Daxxn/BenchyReloaded/Docs/Renders/MotherBoard/BenchyMotherBoard-PCB_Early2-BOT1.png

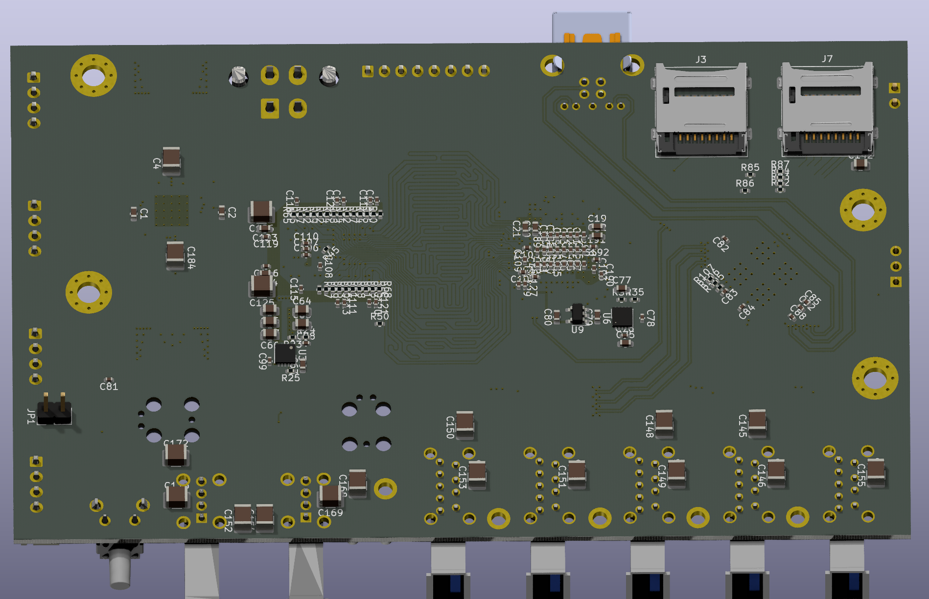
Docs/Renders/MotherBoard/BenchyMotherBoard-PCB_Early2-BOT1.png
