Daxxn/BenchyReloaded/Docs/Renders/MotherBoard/BenchyMotherBoard-PCB_Early3-TOP1.png

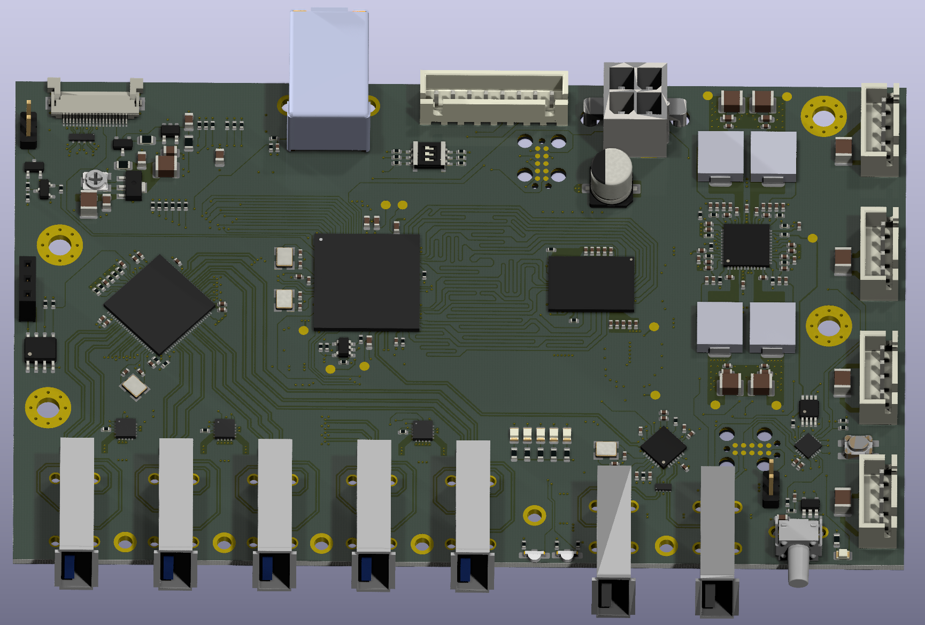
Docs/Renders/MotherBoard/BenchyMotherBoard-PCB_Early3-TOP1.png
