Daxxn/BenchyReloaded/Docs/Renders/MotherBoard/BenchyMotherBoard-PCB_Early-TOP1.png

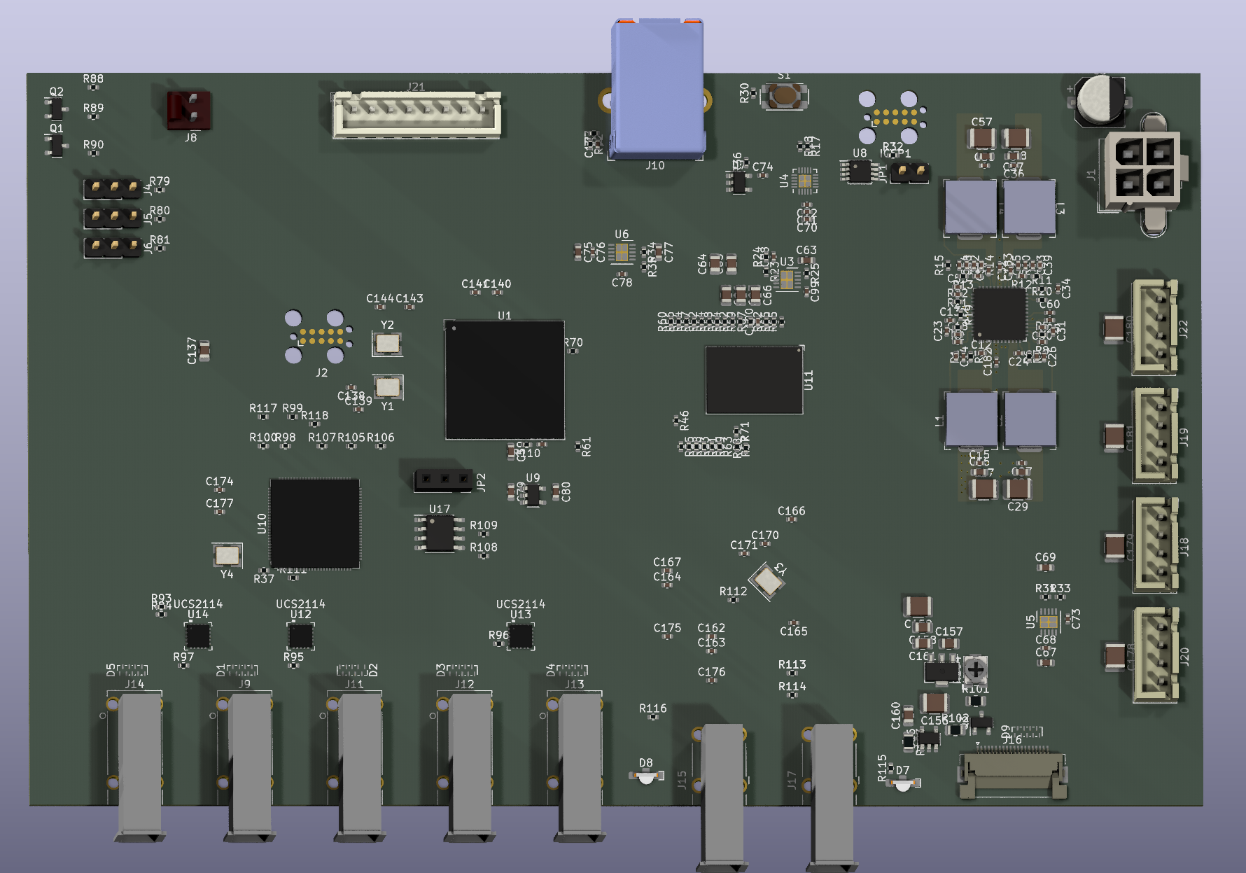
Docs/Renders/MotherBoard/BenchyMotherBoard-PCB_Early-TOP1.png
