Daxxn/BenchyReloaded/Docs/Renders/MotherBoard/BenchyMotherBoard-REV1-MPU.png

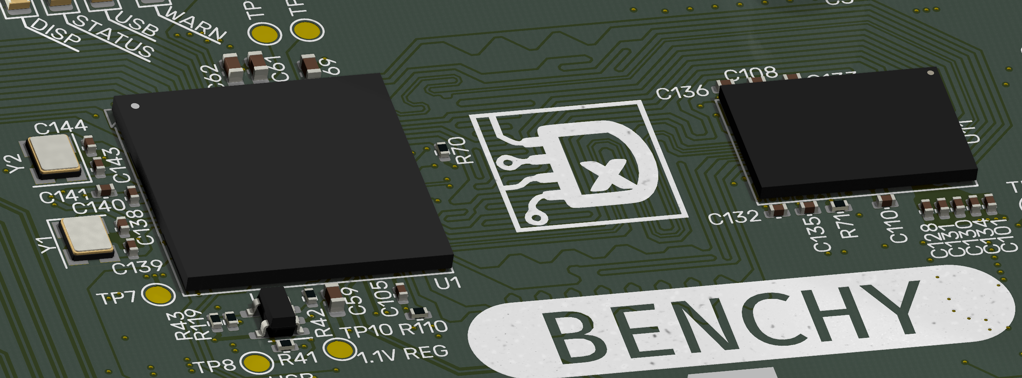
Docs/Renders/MotherBoard/BenchyMotherBoard-REV1-MPU.png
