Daxxn/BenchyReloaded/Docs/Renders/MyPain/BenchyMotherBoard-PCB.png

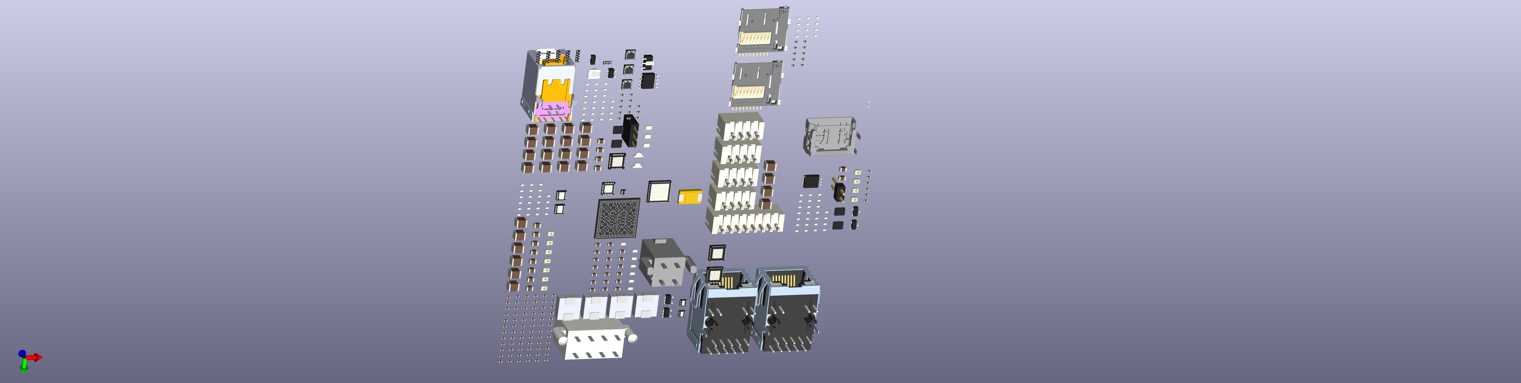
Docs/Renders/MyPain/BenchyMotherBoard-PCB.png
