Daxxn/BenchyReloaded/Docs/Renders/MyPain/JustThePS.JPG

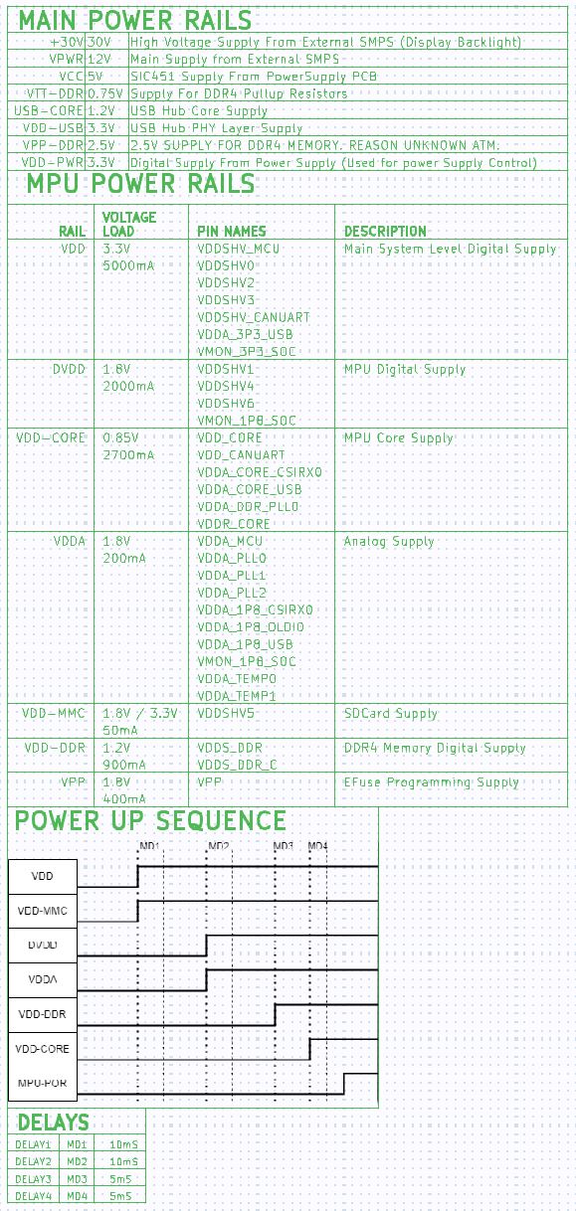
Docs/Renders/MyPain/JustThePS.JPG
