Daxxn/BenchyReloaded/Docs/Renders/Version2/Benchy-Front1.JPG

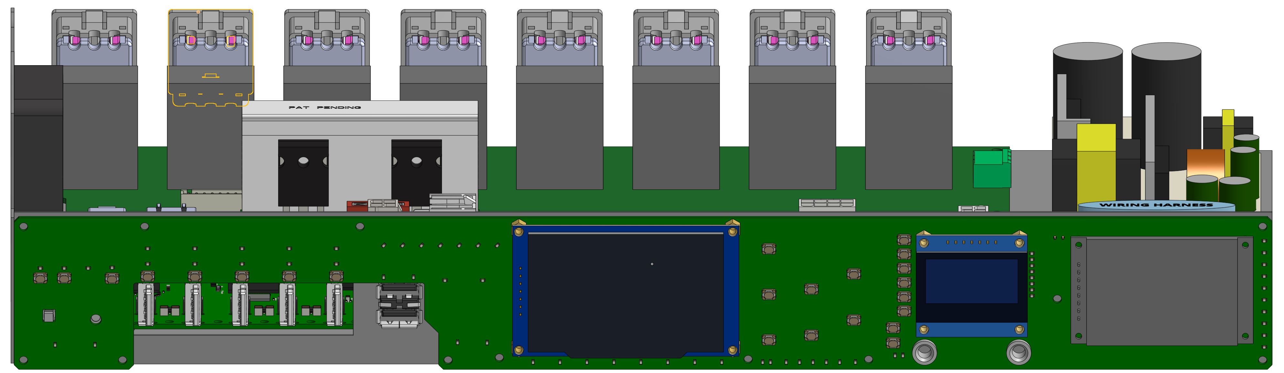
Docs/Renders/Version2/Benchy-Front1.JPG
