Daxxn/BenchyReloaded/Docs/Renders/Version2/Benchy-Top1.JPG

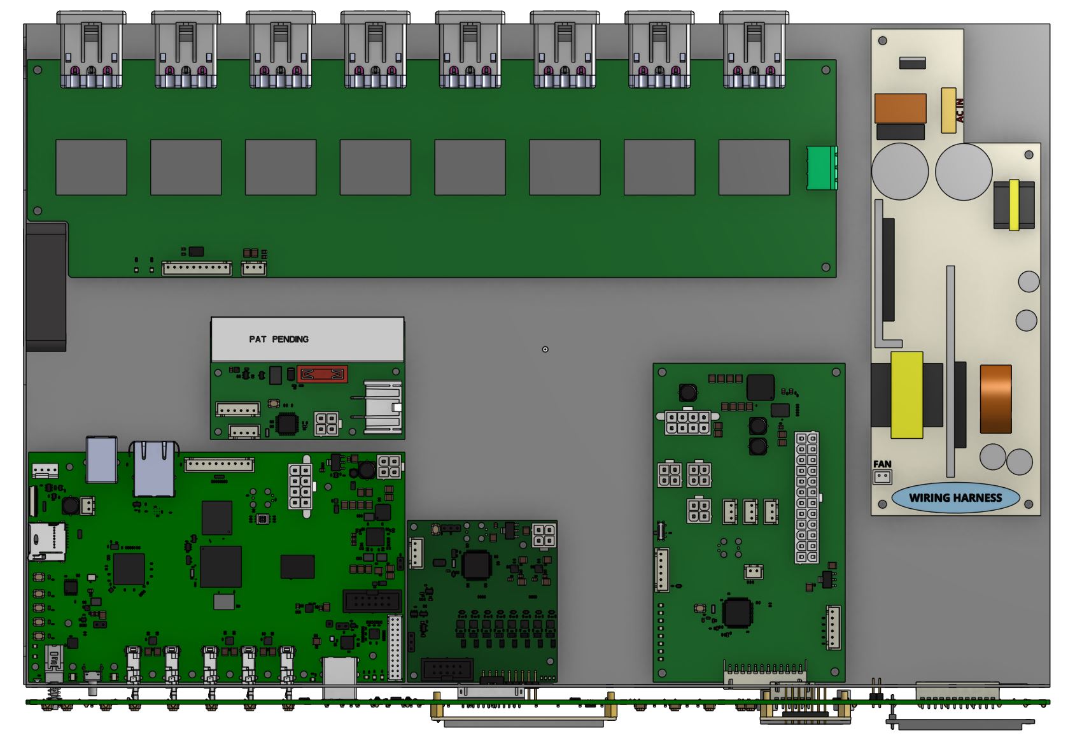
Docs/Renders/Version2/Benchy-Top1.JPG
