Daxxn/BenchyReloaded/Docs/Renders/Version2/BenchyMotherboard-Side1.JPG

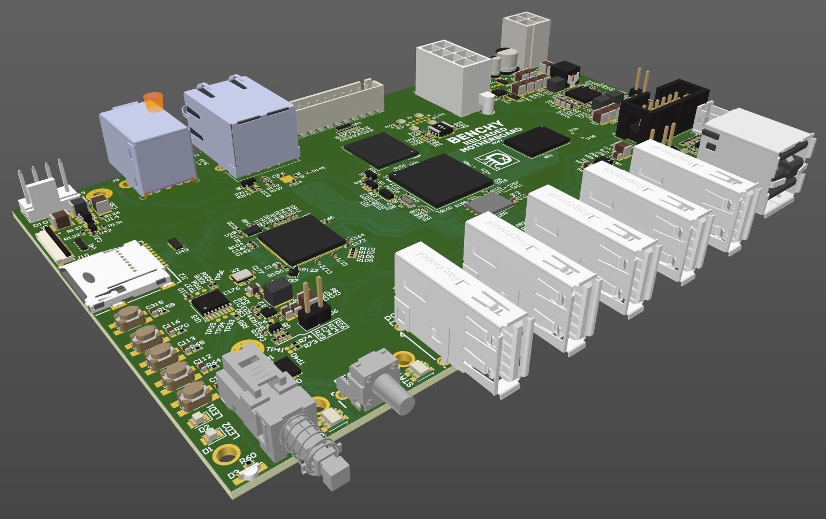
Docs/Renders/Version2/BenchyMotherboard-Side1.JPG
